anno73/IoT-Universal-Socket-Strip/software/controller/src/iotwebconf.cpp

#include <Arduino.h>

#include <string.h>
#include <Streaming.h>

#include <ESP8266HTTPUpdateServer.h>

#include "global.h"

#include "iotwebconf_.h"

#include "mqtt.h"
#include "ota.h"
#include "ntp.h"

// -- Configuration specific key. The value should be modified if config structure was changed.
const char IOTWC_CONFIG_VERSION[] = "REL01";

// -- When BUTTON_PIN is pulled to ground on startup, the Thing will use the initial
//      password to build an AP. (E.g. in case of lost password)
const uint8_t IOTWC_BUTTON_PIN = 2;

// -- Status indicator pin.
//      First it will light up (kept LOW), on Wifi connection it will blink,
//      when connected to the Wifi it will turn off (kept HIGH).
const uint8_t IOTWC_STATUS_PIN = LED_BUILTIN;

DNSServer dnsServer;
ESP8266WebServer webServer(80);
WiFiClient wifiClient;
ESP8266HTTPUpdateServer httpUpdateServer;

// -- Initial name of the Thing. Used e.g. as SSID of the own Access Point.
const char appName[] = "Socket_Strip";

// -- Initial password to connect to the Thing, when it creates an own Access Point.
const char wifiInitialApPassword[] = "12345678";

// -- Method declarations.
void iotWebConfConvertStringParameters(void);

// Callback method declarations - find implementation after IotWebConf initialization
void wifiConnected();
void configSaved();
bool formValidator();

IotWebConf iotWebConf(appName, &dnsServer, &webServer, wifiInitialApPassword, IOTWC_CONFIG_VERSION);

// id, label
iotwebconf::ParameterGroup iotGroupMqtt = iotwebconf::ParameterGroup("groupMqtt", "MQTT Parameters");
// label, id
// valueBuffer, length,
// defaultValue, placeholder, custom HTML
iotwebconf::TextParameter iotMqttServer = iotwebconf::TextParameter(
    "MQTT Server", "mqttServer",
    mqtt::mqttServer, mqtt::MQTT_SERVER_STR_LEN,
    mqtt::mqttServer, mqtt::mqttServer, "");
iotwebconf::NumberParameter iotMqttPort = iotwebconf::NumberParameter(
    "MQTT Port", "mqttPort",
    mqtt::mqttPort, mqtt::MQTT_PORT_STR_LEN,
    mqtt::mqttPort, mqtt::mqttPort, "min='1' max='65535' step='1'");
iotwebconf::TextParameter iotMqttTopicPraefix = iotwebconf::TextParameter(
    "MQTT Topic Praefix", "mqttTopicPraefix",
    mqtt::mqttTopicPraefix, mqtt::MQTT_TOPIC_PRAEFIX_STR_LEN,
    mqtt::mqttTopicPraefix, mqtt::mqttTopicPraefix, "");
iotwebconf::NumberParameter iotMqttHeartbeatInterval = iotwebconf::NumberParameter(
    "MQTT Hearbeat Interval", "mqttHeartbeatInterval",
    mqtt::mqttHeartbeatInterval, mqtt::MQTT_HEARTBEAT_INTERVALL_STR_LEN,
    mqtt::mqttHeartbeatInterval, "in milliseconds", "min='1' max='65535' step='1'");
iotwebconf::NumberParameter iotMqttConnectRetryDelay = iotwebconf::NumberParameter(
    "MQTT connect retry delay", "mqttConnectRetryDelay",
    mqtt::mqttConnectRetryDelay, mqtt::MQTT_CONNECT_RETRY_DELAY_STR_LEN,
    mqtt::mqttConnectRetryDelay, "in milliseconds", "min='1' max='65535' step='1'");
iotwebconf::TextParameter iotMqttTimeTopic = iotwebconf::TextParameter(
    "MQTT Time Topic", "mqttTimeTopic",
    mqtt::mqttTimeTopic, mqtt::MQTT_TIME_TOPIC_STR_LEN,
    mqtt::mqttTimeTopic, mqtt::mqttTimeTopic, "");

iotwebconf::ParameterGroup iotGroupOta = iotwebconf::ParameterGroup("groupOTA", "OTA Parameter");
iotwebconf::PasswordParameter iotOtaUpdatePassword = iotwebconf::PasswordParameter(
    "OTA Update Password", "otaUpdatePassword",
    ota::otaUpdatePassword, ota::OTA_UPDATE_PASWORD_STR_LEN,
    ota::otaUpdatePassword, "");

iotwebconf::ParameterGroup iotGroupNtp = iotwebconf::ParameterGroup("groupNTP", "NTP");
iotwebconf::TextParameter iotNtpServer = iotwebconf::TextParameter(
    "NTP Server", "ntpServer",
    ntp::ntpServer, ntp::NTP_SERVER_STR_LEN,
    ntp::ntpServer, ntp::ntpServer, "");
iotwebconf::NumberParameter iotNtpTzOffset = iotwebconf::NumberParameter(
    "NTP timezone Offset", "ntpTzOffset",
    ntp::ntpTzOffset, ntp::NTP_TZ_OFFSET_STR_LEN,
    ntp::ntpTzOffset, "Timezone Value", "min='-12' max='12' step='1'");

//
// Called from main setup
//
void setupIotWebConf()
{

  Serial << F("Setup IotWebConf") << endl;

  iotGroupMqtt.addItem(&iotMqttServer);
  iotGroupMqtt.addItem(&iotMqttPort);
  iotGroupMqtt.addItem(&iotMqttTopicPraefix);
  iotGroupMqtt.addItem(&iotMqttConnectRetryDelay);
  iotGroupMqtt.addItem(&iotMqttHeartbeatInterval);
  iotGroupMqtt.addItem(&iotMqttTimeTopic);
  iotWebConf.addParameterGroup(&iotGroupMqtt);

  iotGroupOta.addItem(&iotOtaUpdatePassword);
  iotWebConf.addParameterGroup(&iotGroupOta);

  iotGroupNtp.addItem(&iotNtpServer);
  iotGroupNtp.addItem(&iotNtpTzOffset);
  iotWebConf.addParameterGroup(&iotGroupNtp);

  iotWebConf.setStatusPin(IOTWC_STATUS_PIN);
  iotWebConf.setConfigPin(IOTWC_BUTTON_PIN);

  iotWebConf.setConfigSavedCallback(&configSaved);
  iotWebConf.setFormValidator(&formValidator);
  iotWebConf.setWifiConnectionCallback(&wifiConnected);

  //  iotWebConf.setupUpdateServer(&httpUpdateServer);

  iotWebConf.setupUpdateServer(
      [](const char *updatePath) {
        httpUpdateServer.setup(&webServer, updatePath);
      },
      [](const char *userName, char *password) {
        httpUpdateServer.updateCredentials(userName, password);
      });

  // Initialize configuration
  bool validConfig = iotWebConf.init();
  if (!validConfig)
  {
    Serial << F("iotWebConf did not find valid config. Initializing\n");
#if 0
    mqttServer[0] = 0;
    mqttPort[0] = 0;
    mqttTopicPraefix[0] = 0;
    mqttConnectRetryDelay[0] = 0;
    mqttHeartbeatInterval[0] = 0;
    mqttTimeTopic[0] = 0;

    ota::otaUpdatePassword[0] = 0;

    ntpServer[0] = 0;
    ntpTzOffset[0] = 0;
#endif
  }

  // Reduce wait time on boot up
  iotWebConf.setApTimeoutMs(0);

  // Set up required URL handlers on the web server
  webServer.on("/", handleRoot);
  //  webServer.on("/boot", handleBoot);
  webServer.on("/config", [] { iotWebConf.handleConfig(); });
  webServer.onNotFound([]() { iotWebConf.handleNotFound(); });

  iotWebConfConvertStringParameters();

} // setupIotWebConv

//
// Called from main loop.
//
void loopIotWebConf()
{
  iotWebConf.doLoop();
} // loopIotWebconf

//
// Dirty hack to convert strings to integers.
//
void iotWebConfConvertStringParameters()
{

  mqtt::mqttPortInt = atoi(mqtt::mqttPort);

  mqtt::mqttConnectRetryDelayInt = atoi(mqtt::mqttConnectRetryDelay);

  mqtt::mqttHeartbeatIntervalInt = atoi(mqtt::mqttHeartbeatInterval);

  mqtt::mqttTopicPraefixLength = strlen(mqtt::mqttTopicPraefix);

  ntp::ntpTzOffsetInt = atoi(ntp::ntpTzOffset);

} // iotWebConfConvertStringParameters

//
// Respond with root page information.
//
void handleRoot()
{
  if (iotWebConf.handleCaptivePortal())
  {
    // Let IotWebConf test and handle captive portal requests.
    return;
  }

  String s = F("<!DOCTYPE html><html lang=\"en\"><head><meta name=\"viewport\" content=\"width=device-width, initial-scale=1, user-scalable=no\"/><title>");
  s += appName;
  s += F("</title></head><body><h1>MQTT settings</h1><ul><li>MQTT Server: ");
  s += mqtt::mqttServer;
  s += F("<li>MQTT Port: ");
  s += mqtt::mqttPort;
  s += F("<li>MQTT Topic Praefix: ");
  s += mqtt::mqttTopicPraefix;
  s += F("<li>MQTT Connect Retry Delay: ");
  s += mqtt::mqttConnectRetryDelay;

  s += F("</ul><h1>NTP settings</h1><ul><li>NTP Server: ");
  s += ntp::ntpServer;
  s += F("<li>Timezone: ");
  s += ntp::ntpTzOffset;

  s += F("</ul>Go to <a href='config'>configure page</a> to change values.</body></html>\n");

  webServer.send(200, "text/html", s);
} // handleRoot

//
// Request a reboot of the device.
//
void handleBoot()
{
  Serial << F("Reboot requested.\n");
  needReset = true;
} // handleBoot

//
// Callback when WiFi is connected. Triggers some actions
//
void wifiConnected()
{
  Serial << F("WiFi is connected, trigger MQTT and NTP") << endl;
  Serial << F("My IP: ") << WiFi.localIP() << endl;

  mqtt::needConnect = true;
  ntp::needUpdate = true; // could actually work seamless in background with ESP8266 native sntp library

} // wifiConnected

//
// Callback when configuration is saved. Triggers some actions.
//
void configSaved()
{
  Serial << F("Configuration saved. Reboot needed\n");
  // Reboot is the easiest way to utilize new configuration
  needReset = true;
} // configSaved

//
// ToDo: validate configuration parameters.
//
bool formValidator()
{
  Serial << F("Validating form\n");

  bool valid = true;

  // check for digits in numeric values?

  return valid;
} // formValidator
